brockbyte/fpga-audio-mixer/fpga/rtl/mixer_16x2_q14_pipelined_patched.v

// SPDX-License-Identifier: MIT
// Copyright 2025-2026 Sascha Muehlbach
//
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
// ============================================================================
// 16-Channel Stereo Mixer with Q2.14 Gain Coefficients (Pipelined Architecture)
//
// Audio Mixing Algorithm:
// 1) Mute/Solo masking: Each channel multiplied by audibility mask
// 2) Per-channel gains: 16 parallel Q2.14 multipliers (left & right)
// 3) Pipelined summation tree: 4 stages for timing closure at 125 MHz
//    - Stage 0: Register inputs
//    - Stage 1: 16 parallel multiply operations
//    - Stage 2: 4-way summation (groups of 4 channels)
//    - Stage 3: Final 4-to-1 sum + saturation + bus headroom scaling
// 4) Saturation: 24-bit output clipping with configurable headroom
// 5) Bus Headroom: Optional additional attenuation (-6 dB/bit) to prevent clipping
//
// Timing: 3-cycle latency due to pipelining
// ============================================================================
`timescale 1ns / 1ps
`default_nettype none

module mixer_16x2_q14_pipelined #(
    parameter integer SAT_HEADROOM      = 0,  // Saturation-Reserve (wie bisher)
    parameter integer BUS_HEADROOM_BITS = 2   // Additional attenuation on bus (2 ≈ -12 dB)
) (
    input wire clk,
    input wire rst,

    input wire tick,
    input wire ch_valid, // 1-cycle pulse when new 16ch frame is available

    input wire [15:0] solo_button,
    input wire [15:0] mute_button,

    input wire signed [23:0] ch0,
    input wire signed [23:0] ch1,
    input wire signed [23:0] ch2,
    input wire signed [23:0] ch3,
    input wire signed [23:0] ch4,
    input wire signed [23:0] ch5,
    input wire signed [23:0] ch6,
    input wire signed [23:0] ch7,
    input wire signed [23:0] ch8,
    input wire signed [23:0] ch9,
    input wire signed [23:0] ch10,
    input wire signed [23:0] ch11,
    input wire signed [23:0] ch12,
    input wire signed [23:0] ch13,
    input wire signed [23:0] ch14,
    input wire signed [23:0] ch15,

    input wire signed [15:0] g0L,
    input wire signed [15:0] g0R,
    input wire signed [15:0] g1L,
    input wire signed [15:0] g1R,
    input wire signed [15:0] g2L,
    input wire signed [15:0] g2R,
    input wire signed [15:0] g3L,
    input wire signed [15:0] g3R,
    input wire signed [15:0] g4L,
    input wire signed [15:0] g4R,
    input wire signed [15:0] g5L,
    input wire signed [15:0] g5R,
    input wire signed [15:0] g6L,
    input wire signed [15:0] g6R,
    input wire signed [15:0] g7L,
    input wire signed [15:0] g7R,
    input wire signed [15:0] g8L,
    input wire signed [15:0] g8R,
    input wire signed [15:0] g9L,
    input wire signed [15:0] g9R,
    input wire signed [15:0] g10L,
    input wire signed [15:0] g10R,
    input wire signed [15:0] g11L,
    input wire signed [15:0] g11R,
    input wire signed [15:0] g12L,
    input wire signed [15:0] g12R,
    input wire signed [15:0] g13L,
    input wire signed [15:0] g13R,
    input wire signed [15:0] g14L,
    input wire signed [15:0] g14R,
    input wire signed [15:0] g15L,
    input wire signed [15:0] g15R,

    output reg signed [23:0] out_l,
    output reg signed [23:0] out_r,
    output reg               out_valid
);

  // -----------------------------------------------------------------------------
  // Mute/Solo masking
  // -----------------------------------------------------------------------------
  wire solo_active;
  assign solo_active = |solo_button;  // Check if any solo bit is set

  // Per-channel audibility: (no solo active OR channel soloed) AND not muted
  wire [15:0] ch_audible;

  genvar gi;
  generate
    for (gi = 0; gi < 16; gi = gi + 1) begin : GEN_AUDIBLE
      assign ch_audible[gi] = (solo_active ? solo_button[gi] : 1'b1) & ~mute_button[gi];
    end
  endgenerate

  wire signed [23:0] ch_in_eff[0:15];

  assign ch_in_eff[0]  = ch_audible[0] ? ch0 : 24'sd0;
  assign ch_in_eff[1]  = ch_audible[1] ? ch1 : 24'sd0;
  assign ch_in_eff[2]  = ch_audible[2] ? ch2 : 24'sd0;
  assign ch_in_eff[3]  = ch_audible[3] ? ch3 : 24'sd0;
  assign ch_in_eff[4]  = ch_audible[4] ? ch4 : 24'sd0;
  assign ch_in_eff[5]  = ch_audible[5] ? ch5 : 24'sd0;
  assign ch_in_eff[6]  = ch_audible[6] ? ch6 : 24'sd0;
  assign ch_in_eff[7]  = ch_audible[7] ? ch7 : 24'sd0;
  assign ch_in_eff[8]  = ch_audible[8] ? ch8 : 24'sd0;
  assign ch_in_eff[9]  = ch_audible[9] ? ch9 : 24'sd0;
  assign ch_in_eff[10] = ch_audible[10] ? ch10 : 24'sd0;
  assign ch_in_eff[11] = ch_audible[11] ? ch11 : 24'sd0;
  assign ch_in_eff[12] = ch_audible[12] ? ch12 : 24'sd0;
  assign ch_in_eff[13] = ch_audible[13] ? ch13 : 24'sd0;
  assign ch_in_eff[14] = ch_audible[14] ? ch14 : 24'sd0;
  assign ch_in_eff[15] = ch_audible[15] ? ch15 : 24'sd0;

  // ========================
  // Stage -1: Input staging
  // ========================
  reg signed [23:0] st0, st1, st2, st3, st4, st5, st6, st7;
  reg signed [23:0] st8, st9, st10, st11, st12, st13, st14, st15;
  reg have_sample;

  // optional debug
  reg signed [23:0] ch0_reg, ch1_reg;

  // Valid shift register for 3 pipeline stages
  reg [2:0] v_sr;

  always @(posedge clk) begin
    if (rst) begin
      st0 <= 24'd0;
      st1 <= 24'd0;
      st2 <= 24'd0;
      st3 <= 24'd0;
      st4 <= 24'd0;
      st5 <= 24'd0;
      st6 <= 24'd0;
      st7 <= 24'd0;
      st8 <= 24'd0;
      st9 <= 24'd0;
      st10 <= 24'd0;
      st11 <= 24'd0;
      st12 <= 24'd0;
      st13 <= 24'd0;
      st14 <= 24'd0;
      st15 <= 24'd0;
      have_sample <= 1'b0;
    end else begin
      // derzeit: Frame wird nach Verwendung "verbraucht"
      have_sample <= 1'b0;

      if (ch_valid) begin
        ch0_reg <= ch0;
        ch1_reg <= ch1;

        st0 <= ch_in_eff[0];
        st1 <= ch_in_eff[1];
        st2 <= ch_in_eff[2];
        st3 <= ch_in_eff[3];
        st4 <= ch_in_eff[4];
        st5 <= ch_in_eff[5];
        st6 <= ch_in_eff[6];
        st7 <= ch_in_eff[7];
        st8 <= ch_in_eff[8];
        st9 <= ch_in_eff[9];
        st10 <= ch_in_eff[10];
        st11 <= ch_in_eff[11];
        st12 <= ch_in_eff[12];
        st13 <= ch_in_eff[13];
        st14 <= ch_in_eff[14];
        st15 <= ch_in_eff[15];

        have_sample <= 1'b1;
      end
    end
  end

  always @(posedge clk) begin
    if (rst) begin
      v_sr <= 3'b000;
    end else begin
      v_sr <= {v_sr[1:0], have_sample};
    end
  end

  // ========================
  // STAGE 0 → 1: register inputs for multiplies
  // ========================
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
      ) + $signed(
          {{2{pR11[39]}}, pR11}
      );
      aR3 <= $signed(
          {{2{pR12[39]}}, pR12}
      ) + $signed(
          {{2{pR13[39]}}, pR13}
      ) + $signed(
          {{2{pR14[39]}}, pR14}
      ) + $signed(
          {{2{pR15[39]}}, pR15}
      );
    end
  end

  // ========================
  // STAGE 3: final sum, scale, saturate, register output
  // ========================
  wire signed [43:0] bL = $signed(
      {{2{aL0[41]}}, aL0}
  ) + $signed(
      {{2{aL1[41]}}, aL1}
  ) + $signed(
      {{2{aL2[41]}}, aL2}
  ) + $signed(
      {{2{aL3[41]}}, aL3}
  );
  wire signed [43:0] bR = $signed(
      {{2{aR0[41]}}, aR0}
  ) + $signed(
      {{2{aR1[41]}}, aR1}
  ) + $signed(
      {{2{aR2[41]}}, aR2}
  ) + $signed(
      {{2{aR3[41]}}, aR3}
  );

  // Q2.14 scale + additional bus headroom attenuation
  // 14 = Fractionalbits der Q2.14-Gains
  // BUS_HEADROOM_BITS = additional global attenuation (per bit approx -6 dB)
  wire signed [43:0] mixL_q = bL >>> (14 + BUS_HEADROOM_BITS);
  wire signed [43:0] mixR_q = bR >>> (14 + BUS_HEADROOM_BITS);

  // Saturation helpers
  localparam signed [31:0] POS_MAX = 32'sh007FFFFF;
  localparam signed [31:0] NEG_MIN = -32'sh00800000;
  localparam signed [31:0] POS_MAX_HR = (SAT_HEADROOM == 0) ? POS_MAX : (POS_MAX >>> SAT_HEADROOM);
  localparam signed [31:0] NEG_MIN_HR = (SAT_HEADROOM == 0) ? NEG_MIN : (NEG_MIN >>> SAT_HEADROOM);

  function [23:0] sat24_hr;
    input signed [43:0] v;
    reg signed [31:0] vv;
    begin
      if (v > POS_MAX_HR) vv = POS_MAX_HR;
      else if (v < NEG_MIN_HR) vv = NEG_MIN_HR;
      else vv = v[31:0];
      sat24_hr = vv[23:0];
    end
  endfunction

  always @(posedge clk) begin
    if (rst) begin
      out_l     <= 24'd0;
      out_r     <= 24'd0;
      out_valid <= 1'b0;
    end else begin
      out_valid <= v_sr[2];  // Third pipeline stage

      if (v_sr[2]) begin
        out_l <= sat24_hr(mixL_q);
        out_r <= sat24_hr(mixR_q);
      end
    end
  end

endmodule

`resetall
`default_nettype wire
